ifilot/parametric-dip-socket-tray/exports/dip28-label.stl

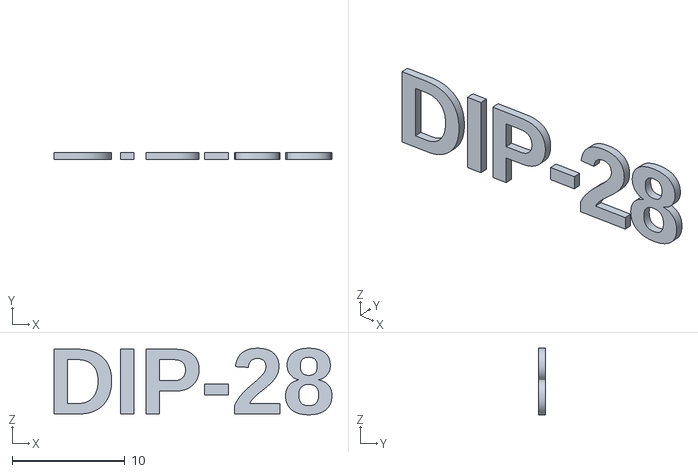
[picture p22: CAD file, 2026-08-31]
exports/dip28-label.stl
24.6 x 0.62 x 5.90
