ifilot/parametric-dip-socket-tray/exports/dip28-fit-test.stl

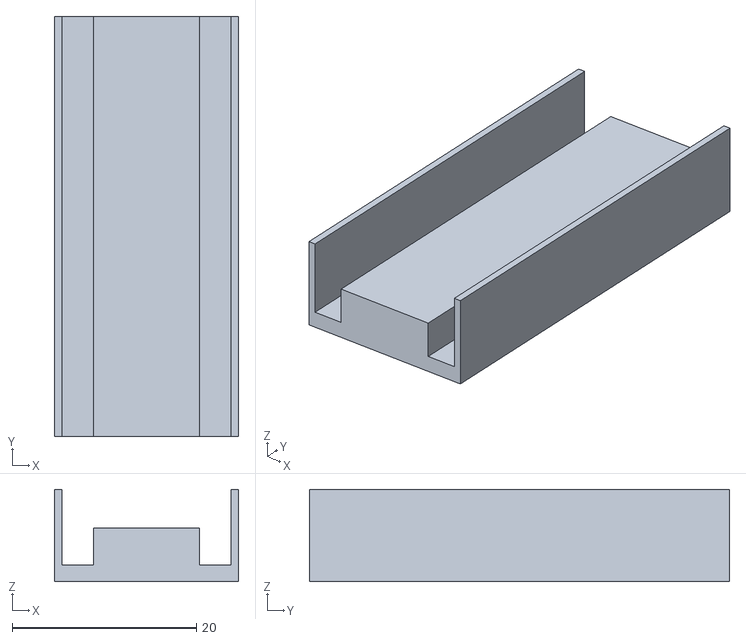
[picture p23: CAD file, 2026-08-30]
exports/dip28-fit-test.stl
20.0 x 45.6 x 10.0
