ifilot/parametric-dip-socket-tray/exports/dip16-fit-test.stl

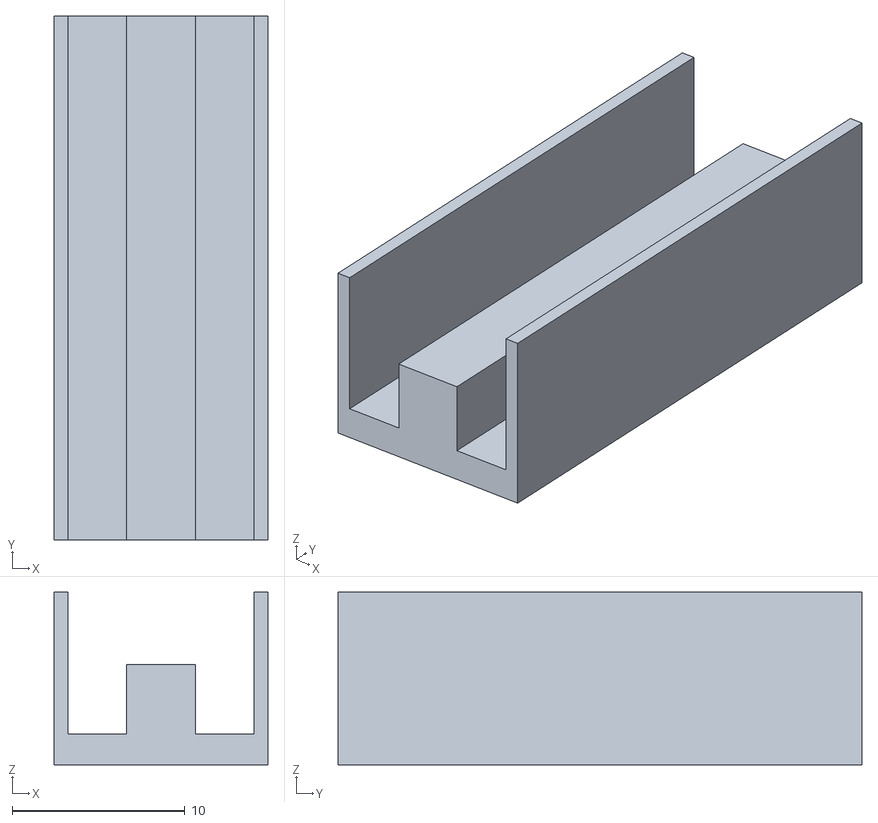
[picture p24: CAD file, 2026-08-30]
exports/dip16-fit-test.stl
12.4 x 30.3 x 10.0
