ifilot/parametric-dip-socket-tray/exports/dip40-fit-test.stl

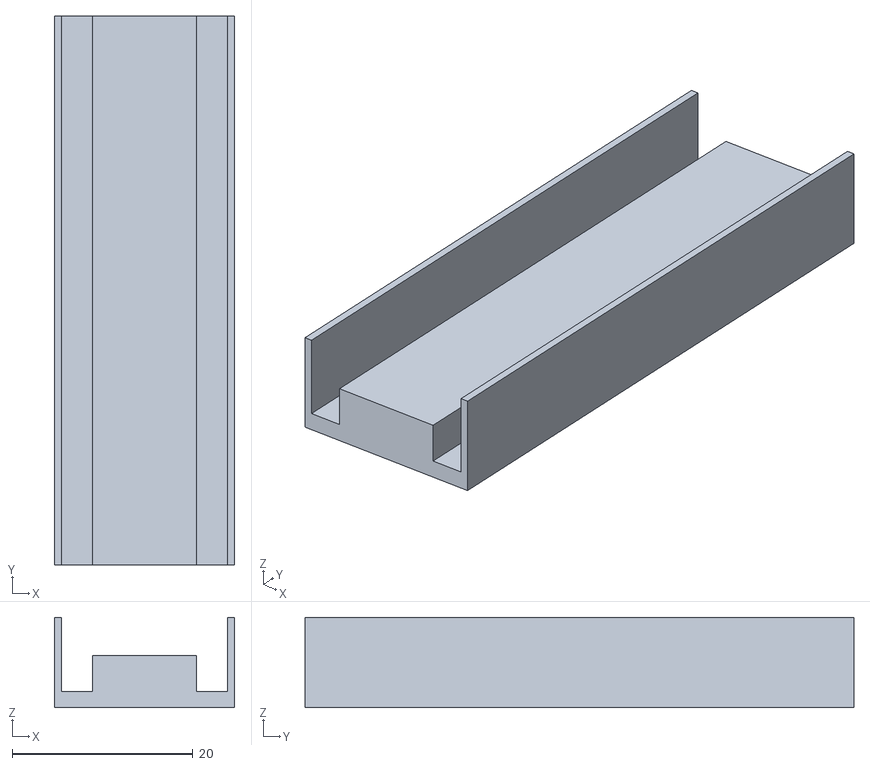
[picture p25: CAD file, 2026-08-30]
exports/dip40-fit-test.stl
20.0 x 60.8 x 10.0
