ifilot/parametric-dip-socket-tray/exports/dip32-fit-test.stl

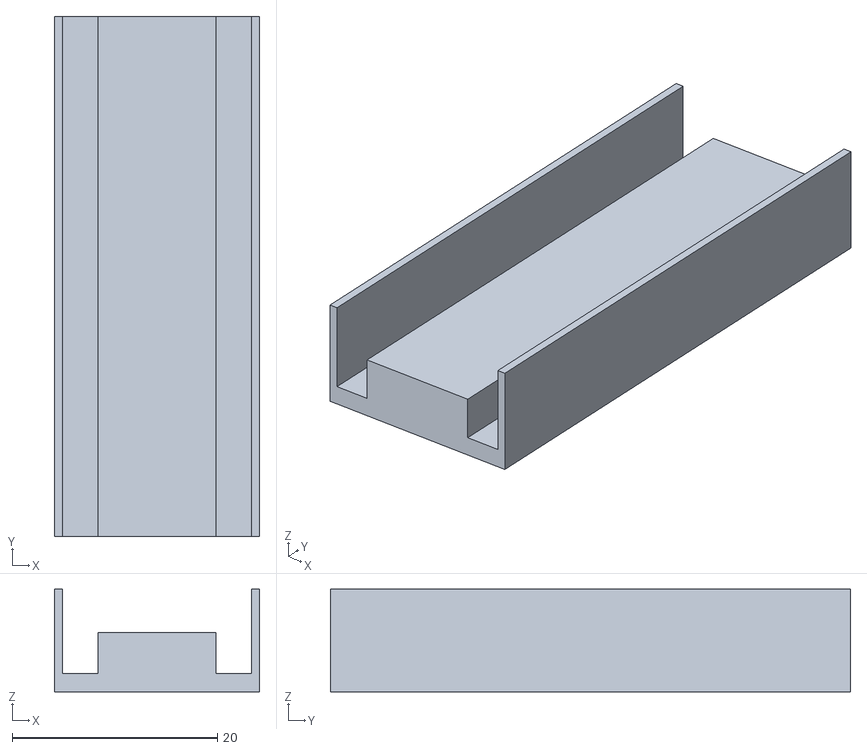
[picture p26: CAD file, 2026-08-30]
exports/dip32-fit-test.stl
20.0 x 50.6 x 10.0
