ifilot/parametric-dip-socket-tray/exports/dip18-fit-test.stl

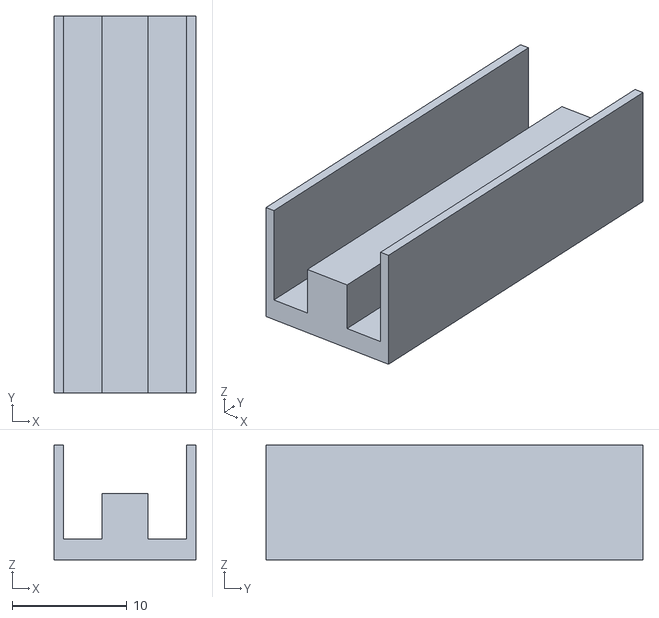
[picture p27: CAD file, 2026-08-30]
exports/dip18-fit-test.stl
12.4 x 32.9 x 10.0
