ifilot/parametric-dip-socket-tray/exports/dip14-fit-test.stl

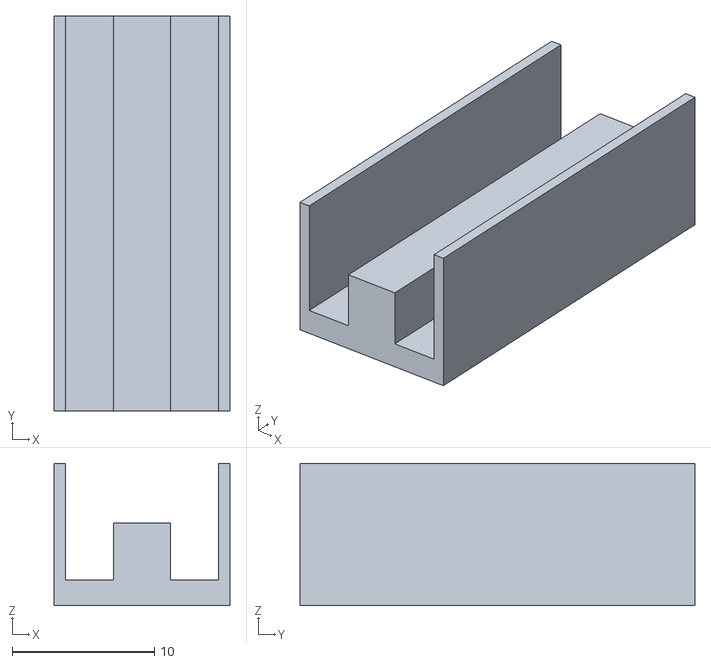
[picture p28: CAD file, 2026-08-30]
exports/dip14-fit-test.stl
12.4 x 27.8 x 10.0
