ifilot/parametric-dip-socket-tray/exports/dip20-fit-test.stl

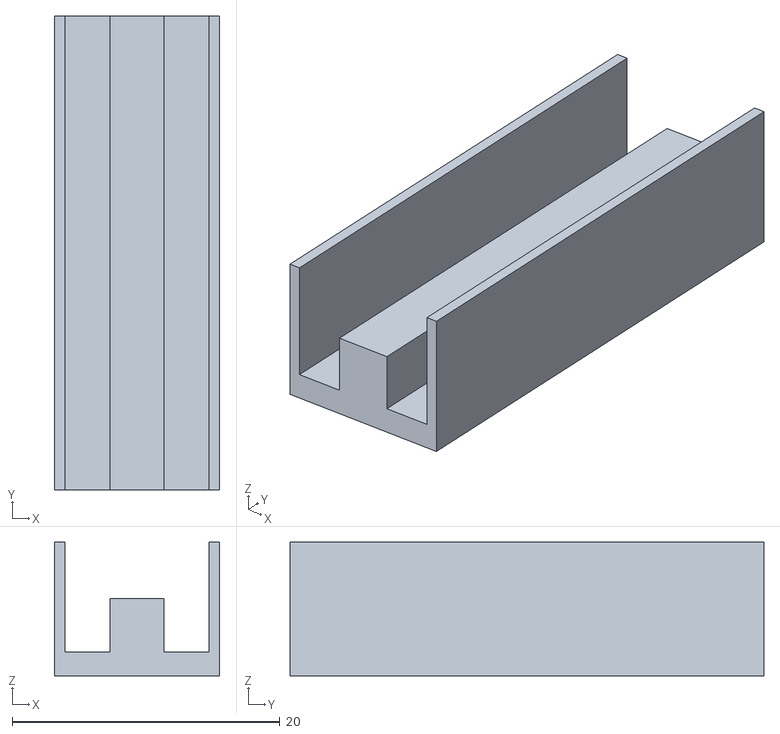
[picture p29: CAD file, 2026-08-30]
exports/dip20-fit-test.stl
12.4 x 35.4 x 10.0
